davinmln/Smart-Parking/3D Design/File 3D/3D Jadi 3.jpg

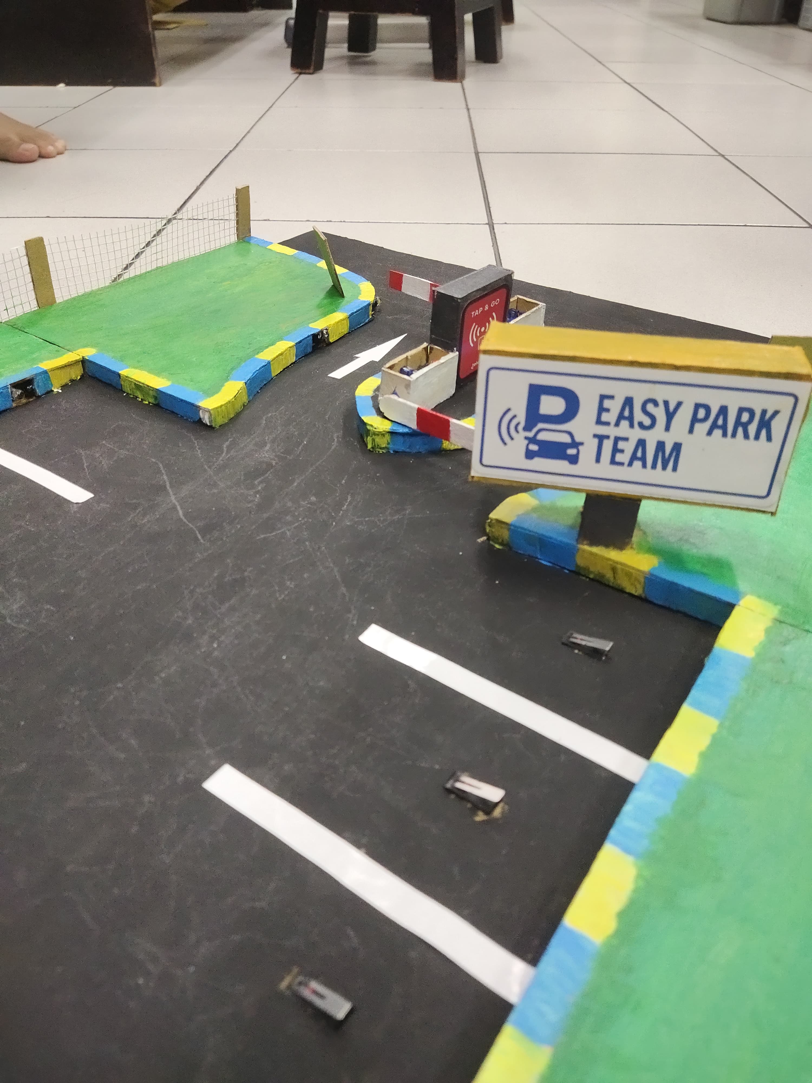
3D Design/File 3D/3D Jadi 3.jpg
