davinmln/Smart-Parking/Image/Blok Diagram.jpg

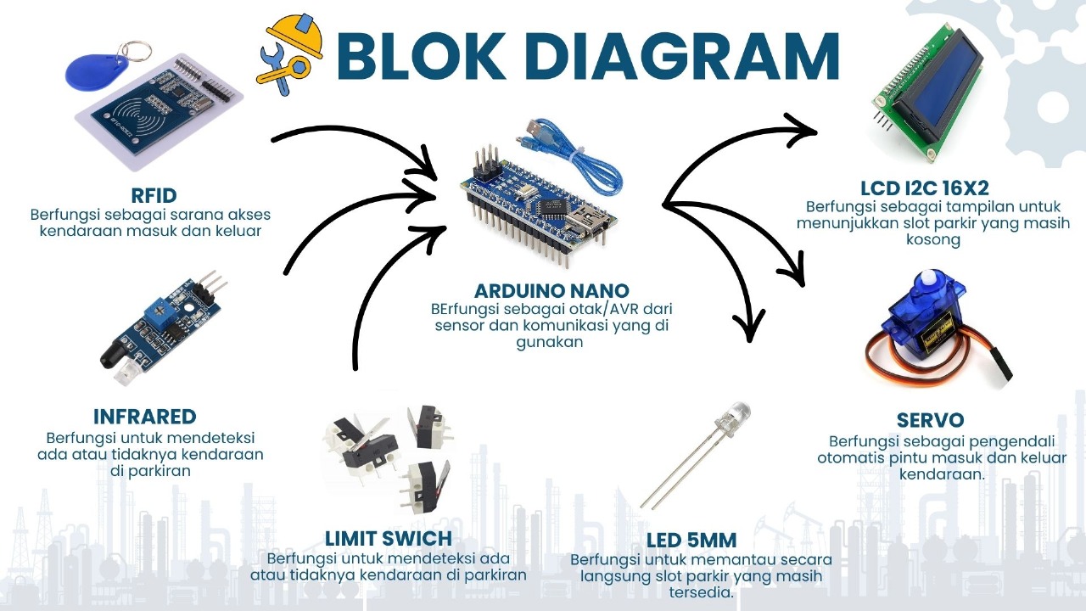
Image/Blok Diagram.jpg
